somhi/MiSTdon/references/Jepalza/P1010012.JPG

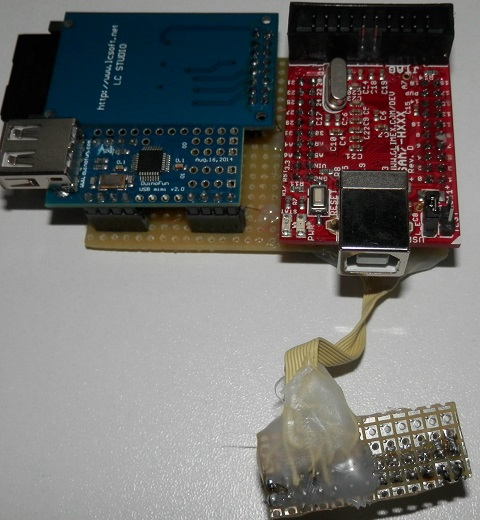
references/Jepalza/P1010012.JPG
